aroum/PNCATEHO/doc/img/preview/3d_preview.jpg

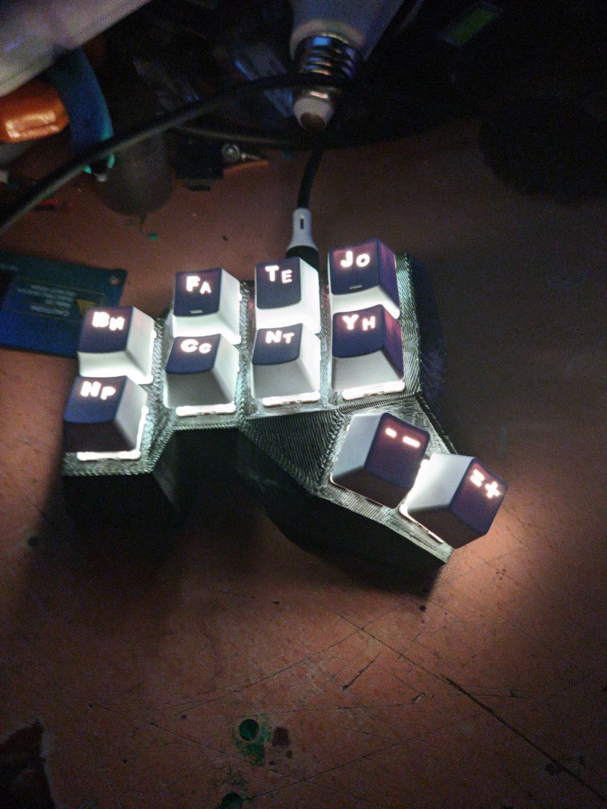
doc/img/preview/3d_preview.jpg
