aroum/PNCATEHO/doc/img/socket/machine_back.jpg

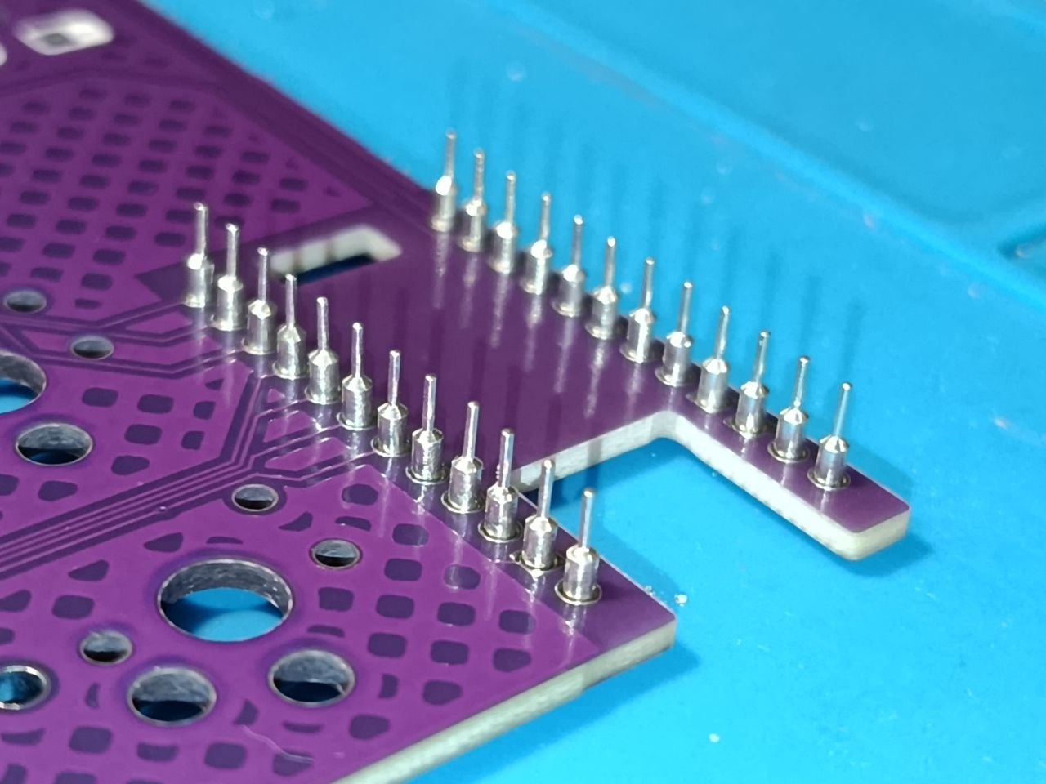
doc/img/socket/machine_back.jpg
