aroum/PNCATEHO/doc/img/socket/machine_back_mcu.jpg

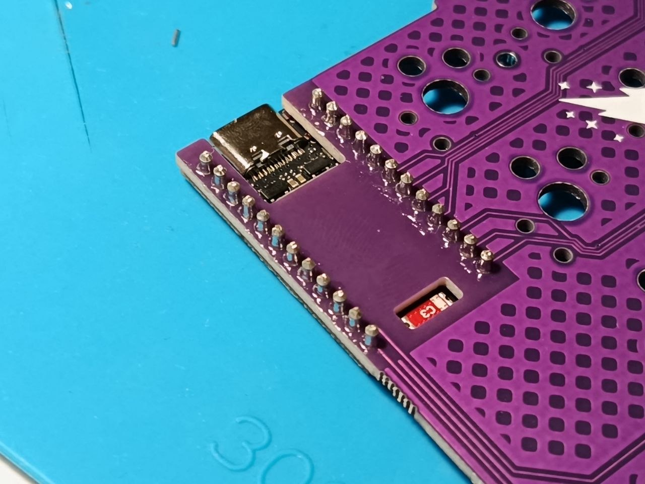
doc/img/socket/machine_back_mcu.jpg
