aroum/PNCATEHO/doc/img/socket/machine_back_strip.jpg

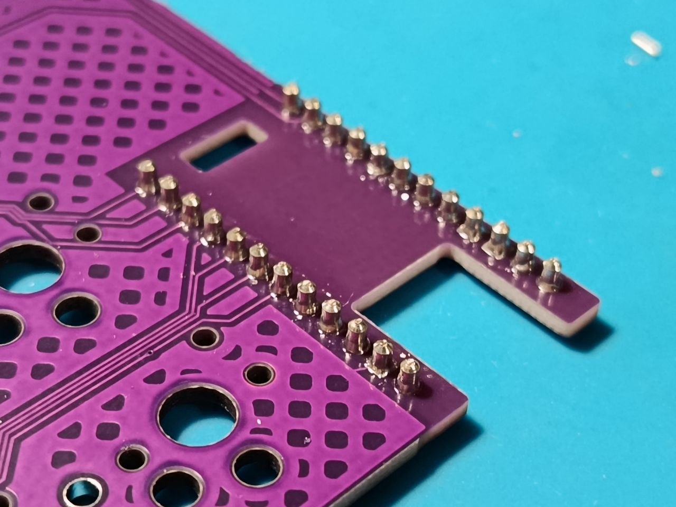
doc/img/socket/machine_back_strip.jpg
