aroum/PNCATEHO/doc/img/socket/machine_row.jpg

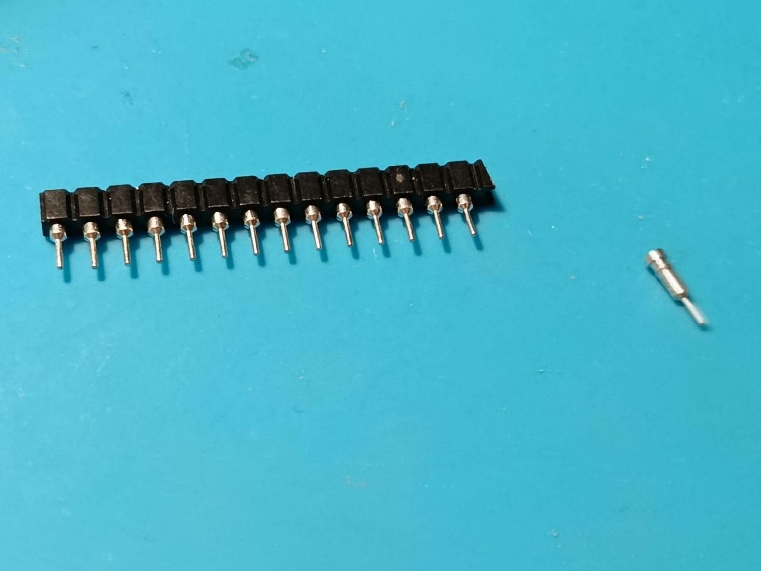
doc/img/socket/machine_row.jpg
