aroum/PNCATEHO/doc/img/socket/machine_top.jpg

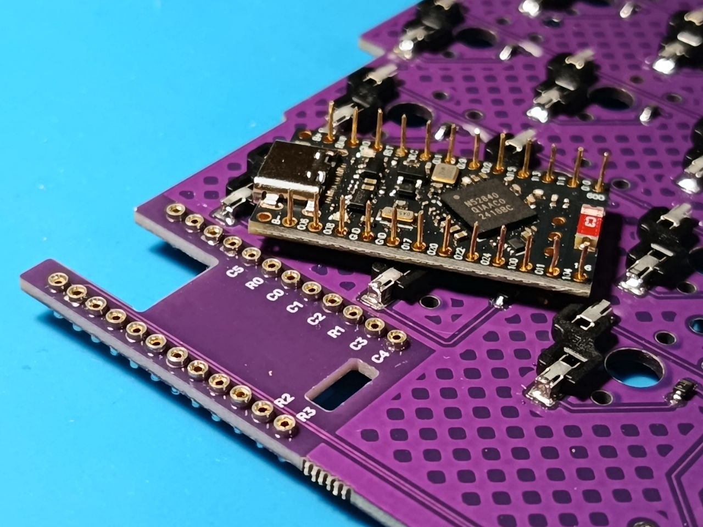
doc/img/socket/machine_top.jpg
