aroum/PNCATEHO/doc/img/socket/machine_top_mcu.jpg

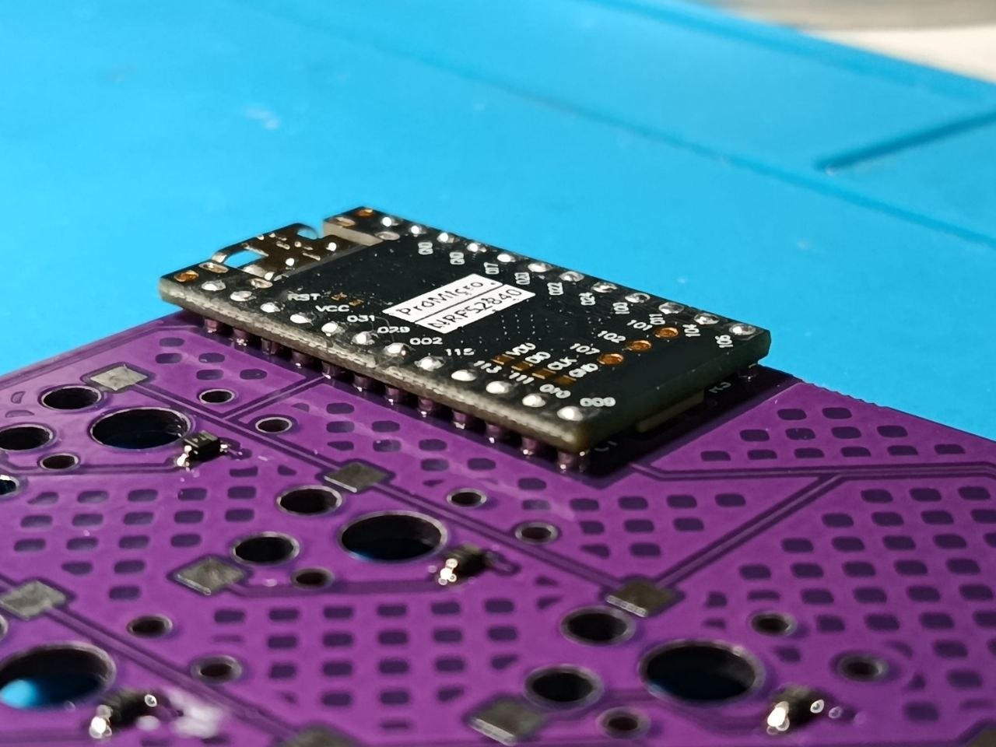
doc/img/socket/machine_top_mcu.jpg
