aroum/PNCATEHO/light/welcome/pcb/PNCATEHO_lib/step/SW_SPST_B3U-1000P-B.step

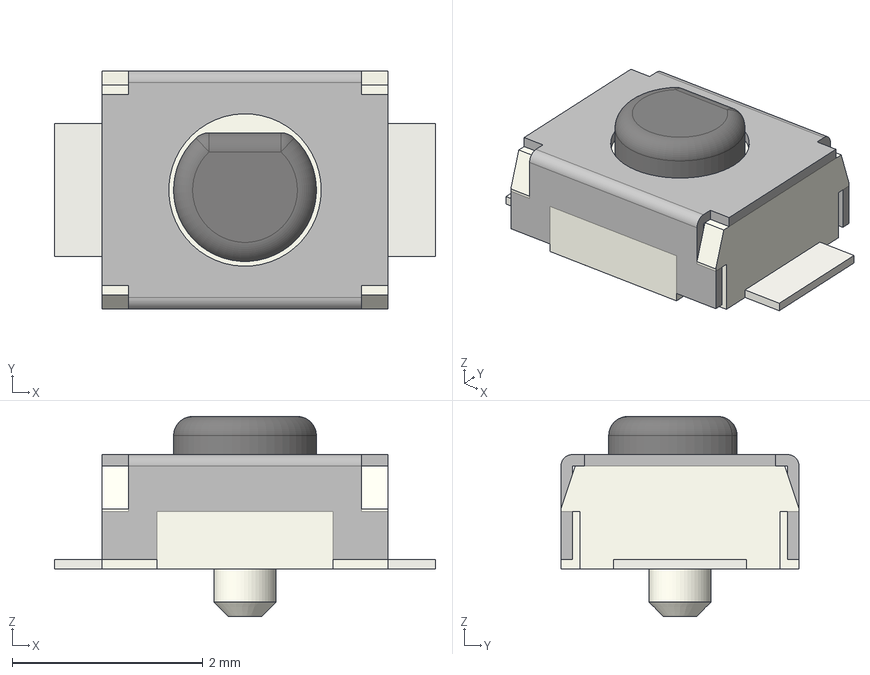
[picture p39: CAD file, 2026-05-25]
light/welcome/pcb/PNCATEHO_lib/step/SW_SPST_B3U-1000P-B.step
4.00 x 2.50 x 2.10 mm
