aroum/PNCATEHO/glass/case/MK_DOSE/PNCATEHO_MK_DOSE-case-bottom-right.step

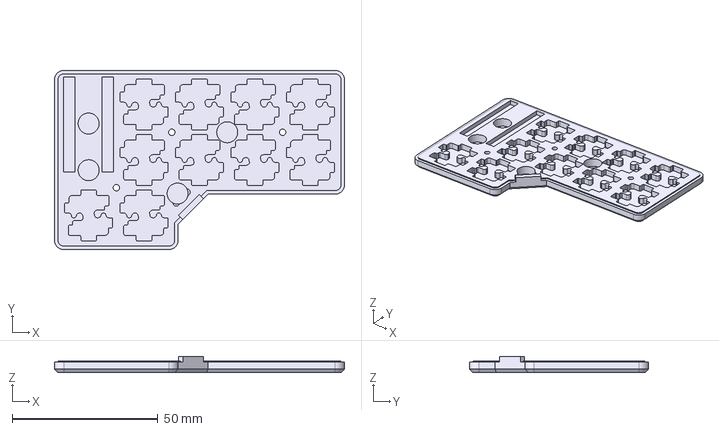
[picture p40: CAD file, 2025-08-24]
glass/case/MK_DOSE/PNCATEHO_MK_DOSE-case-bottom-right.step
99.4 x 61.4 x 5.60 mm
