aroum/PNCATEHO/glass/case/v5/PNCATEHO_v5-top-cover-left-PNCATEHO-ReggageOne.step

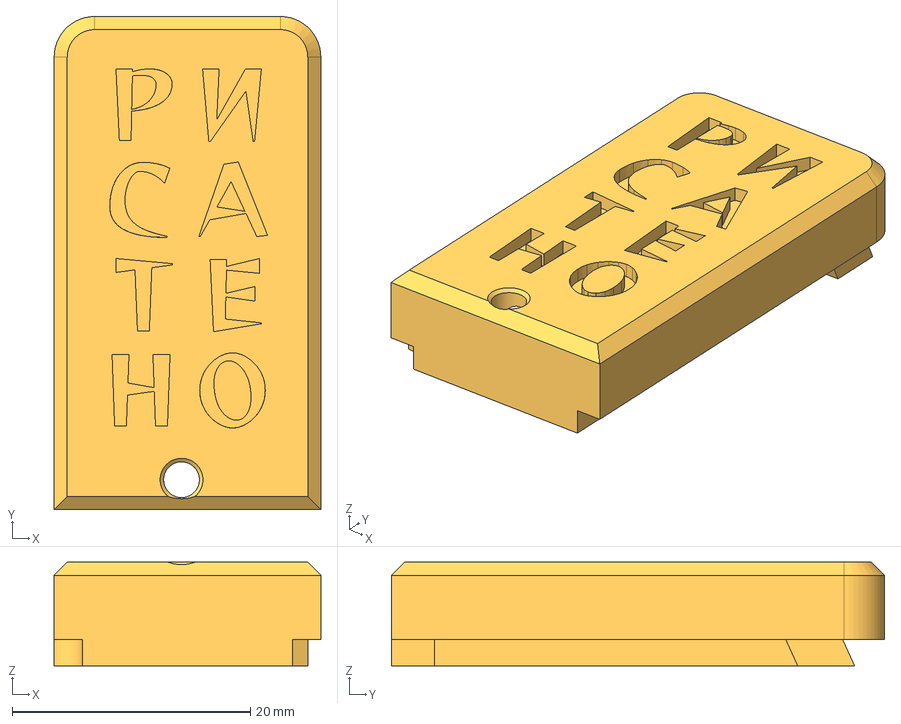
[picture p41: CAD file, 2025-06-07]
glass/case/v5/PNCATEHO_v5-top-cover-left-PNCATEHO-ReggageOne.step
22.4 x 41.4 x 8.70 mm
