aroum/PNCATEHO/light/welcome/pcb/PNCATEHO_lib/step/LED_0805_2012Metric.step

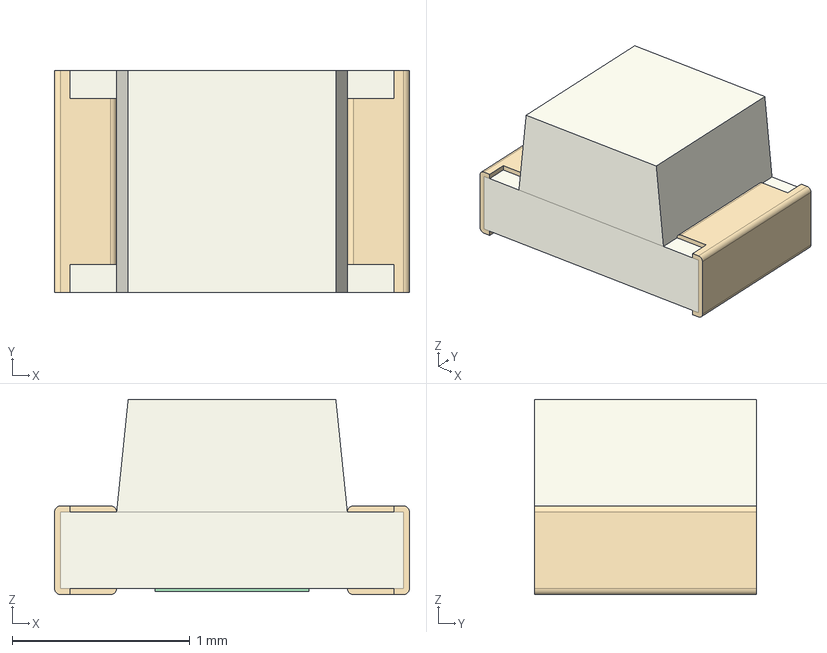
[picture p42: CAD file, 2026-05-25]
light/welcome/pcb/PNCATEHO_lib/step/LED_0805_2012Metric.step
2.00 x 1.25 x 1.10 mm
