aroum/PNCATEHO/light/welcome/pcb/PNCATEHO_lib/step/D_0805_2012Metric.step

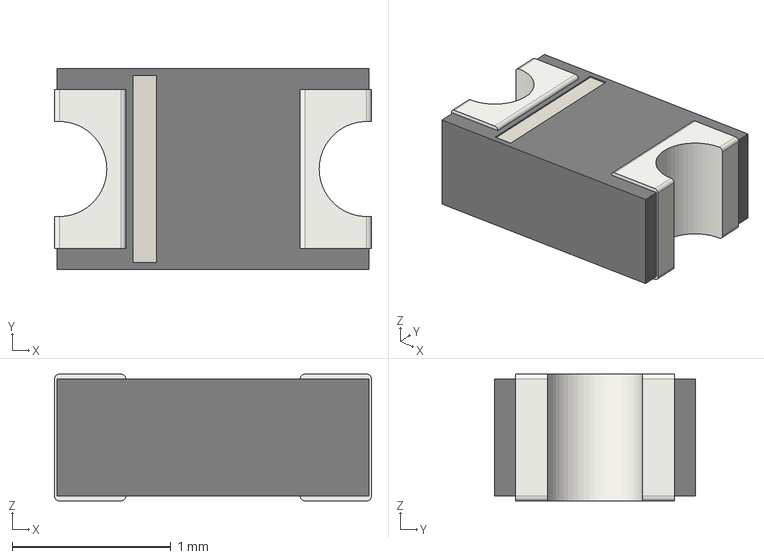
[picture p43: CAD file, 2026-05-25]
light/welcome/pcb/PNCATEHO_lib/step/D_0805_2012Metric.step
2.00 x 1.27 x 0.8 mm
