aroum/PNCATEHO/glass/case/MK_DOSE/PNCATEHO_MK_DOSE-case-top-left.step

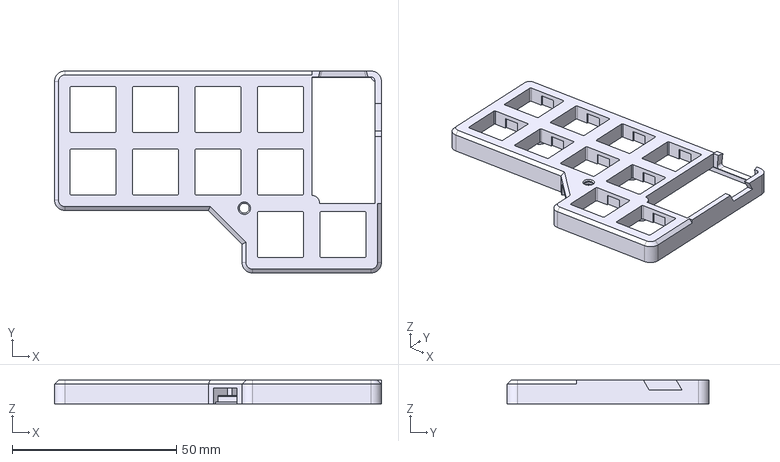
[picture p44: CAD file, 2025-08-12]
glass/case/MK_DOSE/PNCATEHO_MK_DOSE-case-top-left.step
99.4 x 61.4 x 7.20 mm
