aroum/PNCATEHO/glass/case/v5/PNCATEHO_v5-reset-button-pusher.step

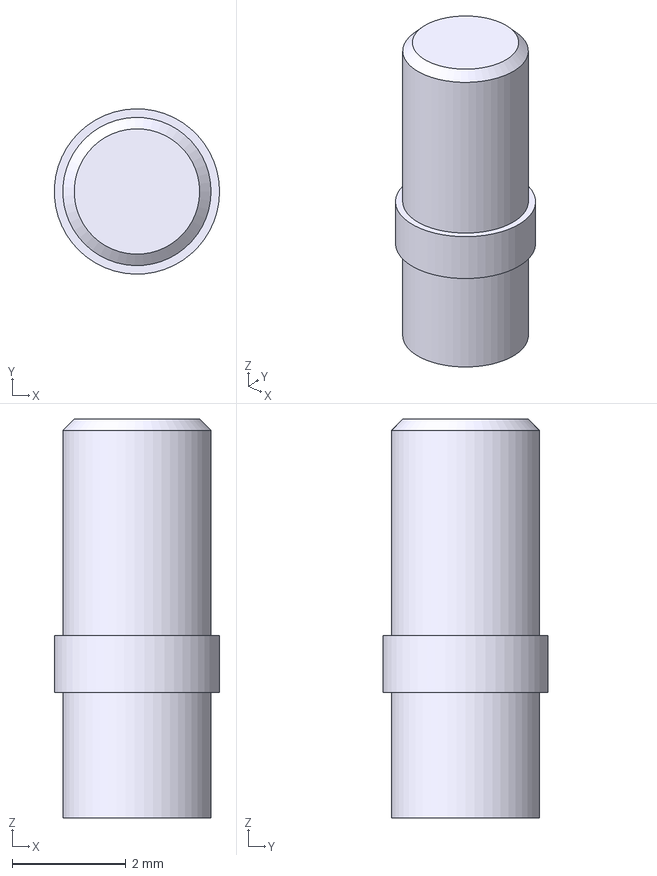
[picture p45: CAD file, 2025-06-07]
glass/case/v5/PNCATEHO_v5-reset-button-pusher.step
2.90 x 2.90 x 7.00 mm
