aroum/PNCATEHO/light/welcome/pcb/PNCATEHO_lib/step/R_0805_2012Metric.step

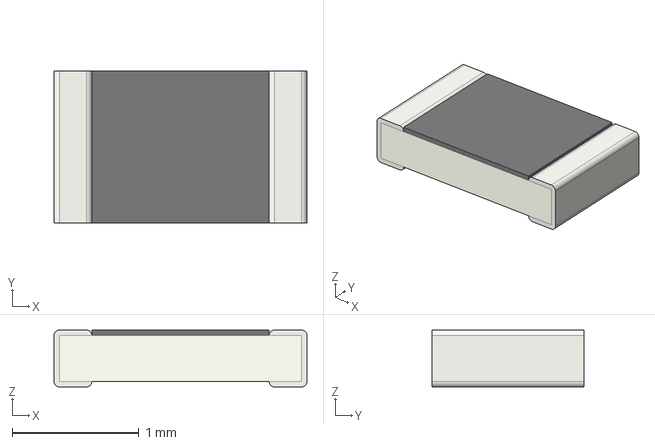
[picture p46: CAD file, 2026-05-25]
light/welcome/pcb/PNCATEHO_lib/step/R_0805_2012Metric.step
2.00 x 1.20 x 0.45 mm
