aroum/PNCATEHO/glass/case/MK_DOSE/PNCATEHO_MK_DOSE-case-top-cover-JP-katakana-right.step

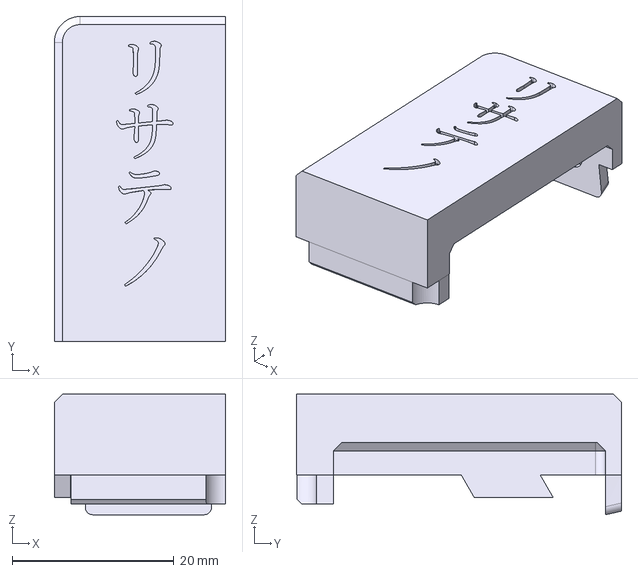
[picture p47: CAD file, 2025-08-12]
glass/case/MK_DOSE/PNCATEHO_MK_DOSE-case-top-cover-JP-katakana-right.step
21.2 x 40.2 x 14.9 mm
