aroum/PNCATEHO/glass/case/v5/PNCATEHO_v5-top-cover-right-blank.step

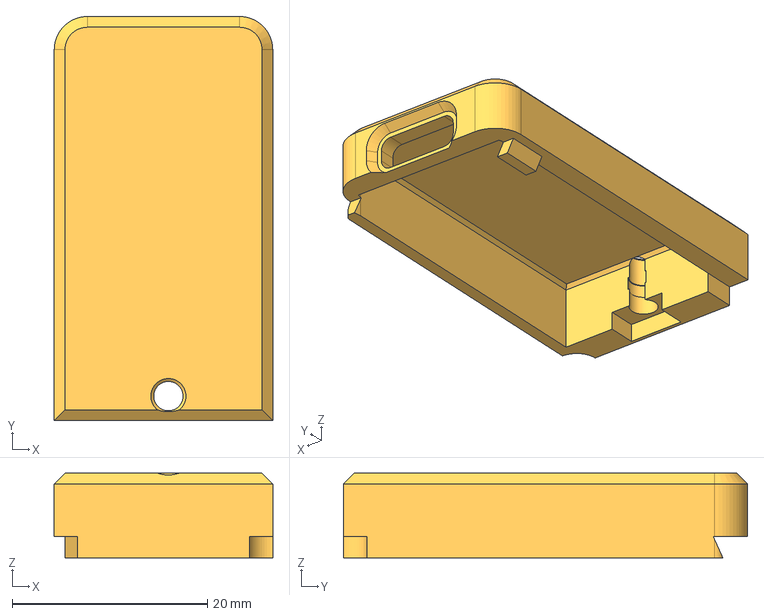
[picture p48: CAD file, 2025-06-07]
glass/case/v5/PNCATEHO_v5-top-cover-right-blank.step
22.4 x 41.4 x 8.70 mm
