aroum/PNCATEHO/light/welcome/pcb/PNCATEHO_lib/step/RT9013-33GB.STEP

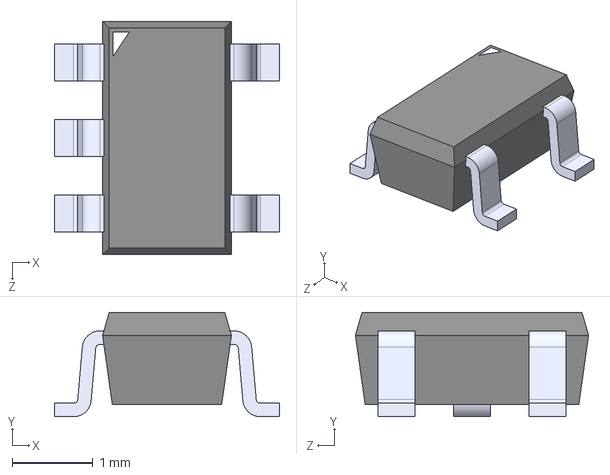
[picture p49: CAD file, 2026-05-25]
light/welcome/pcb/PNCATEHO_lib/step/RT9013-33GB.STEP
2.79 x 1.30 x 2.90 mm
