aroum/PNCATEHO/light/welcome/pcb/PNCATEHO_lib/step/PG1316S.STEP

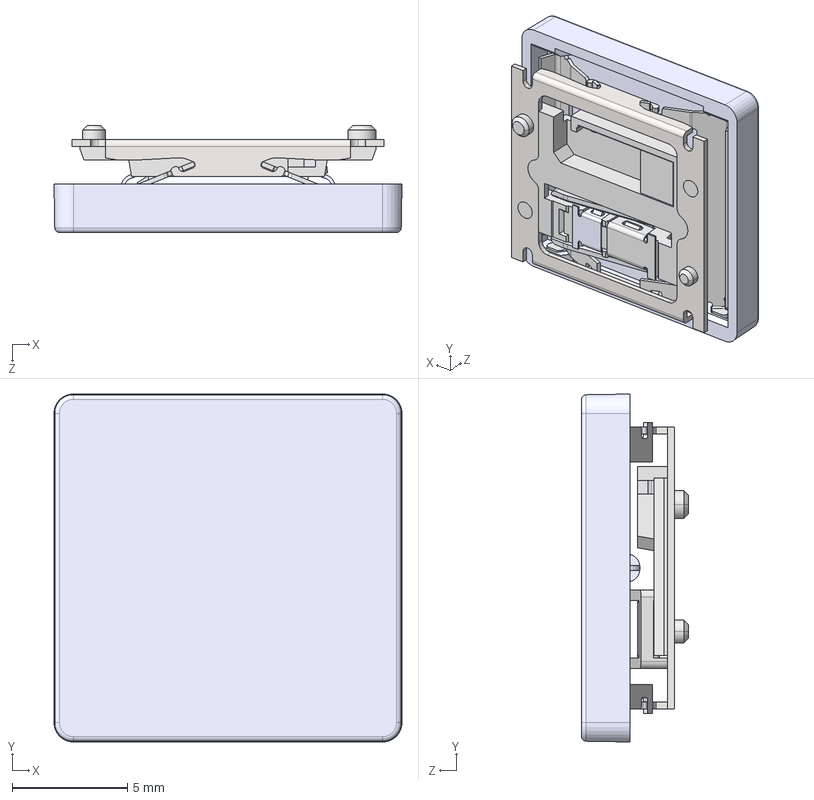
[picture p50: CAD file, 2026-05-25]
light/welcome/pcb/PNCATEHO_lib/step/PG1316S.STEP
15.1 x 15.1 x 4.63 mm
1316S-基座卡件
PG1316S-價釱
驱动杆
す算殤
嶺銅
PG1316S-动接触片-带触点
PG1316S-静片-带触点
す算殤-B
瑩簽
