aroum/PNCATEHO/glass/case/MK_DOSE/PNCATEHO_MK_DOSE-case-top-cover-blank-left.step

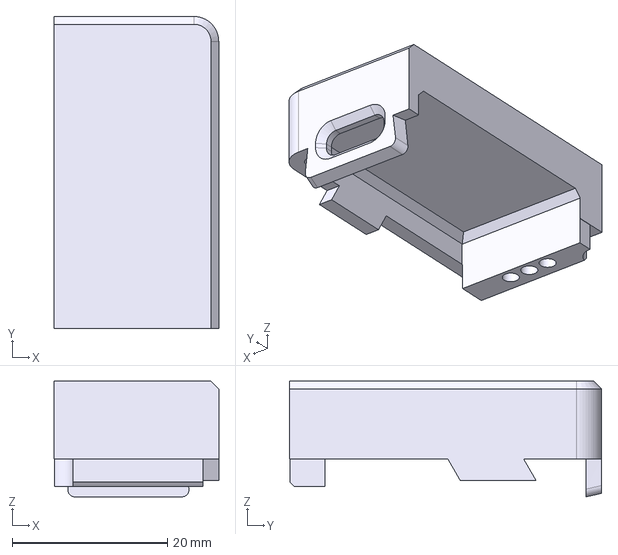
[picture p51: CAD file, 2025-08-12]
glass/case/MK_DOSE/PNCATEHO_MK_DOSE-case-top-cover-blank-left.step
21.2 x 40.2 x 14.9 mm
