aroum/PNCATEHO/light/welcome/pcb/PNCATEHO_lib/step/Crystal_SMD_3225-4Pin_3.2x2.5mm.step

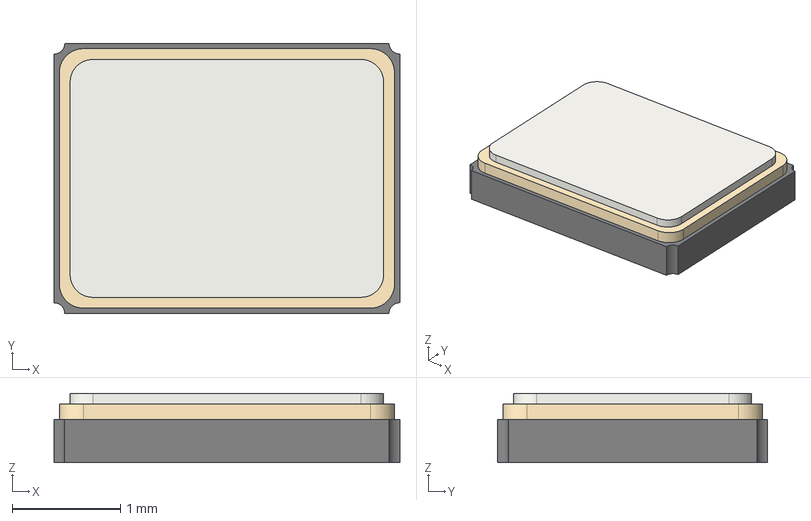
[picture p52: CAD file, 2026-05-25]
light/welcome/pcb/PNCATEHO_lib/step/Crystal_SMD_3225-4Pin_3.2x2.5mm.step
3.20 x 2.50 x 0.64 mm
