aroum/PNCATEHO/glass/case/v5/PNCATEHO_v5-power-switch-pusher.step

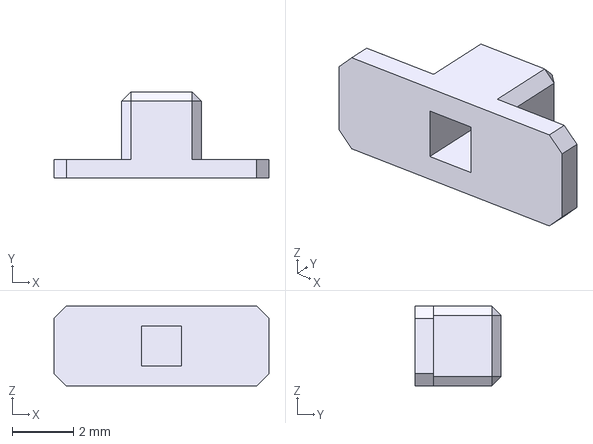
[picture p53: CAD file, 2025-06-07]
glass/case/v5/PNCATEHO_v5-power-switch-pusher.step
7.00 x 2.80 x 2.60 mm
