aroum/PNCATEHO/light/welcome/pcb/PNCATEHO_lib/step/QFN-56-1EP_7x7mm_P0.4mm_EP4x4mm.step

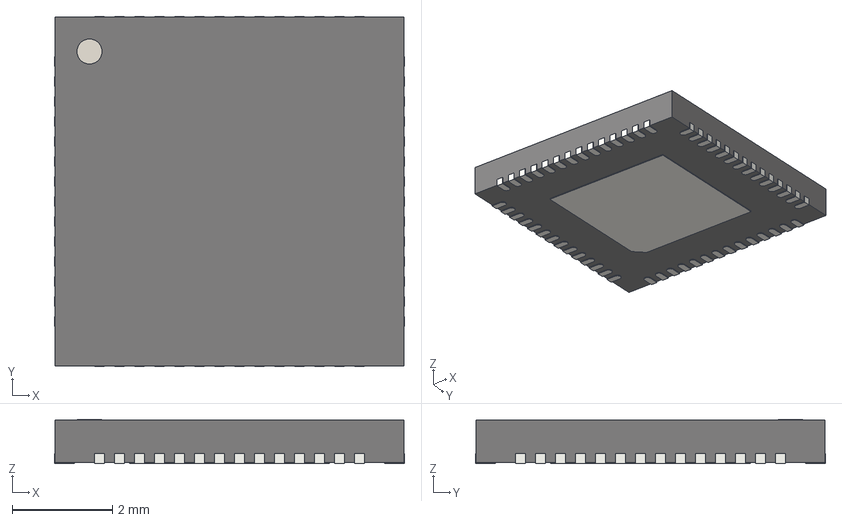
[picture p54: CAD file, 2026-05-25]
light/welcome/pcb/PNCATEHO_lib/step/QFN-56-1EP_7x7mm_P0.4mm_EP4x4mm.step
7.00 x 7.00 x 0.885 mm
a48c614c-8773-11ed-8f9d-58fb8493fcfb_part
a48c63fe-8773-11ed-8f9d-58fb8493fcfb_part
a48c65a2-8773-11ed-8f9d-58fb8493fcfb_part
a48c66d8-8773-11ed-8f9d-58fb8493fcfb_part
