aroum/PNCATEHO/glass/case/MK_DOSE/PNCATEHO_MK_DOSE-reset-button-pusher.step

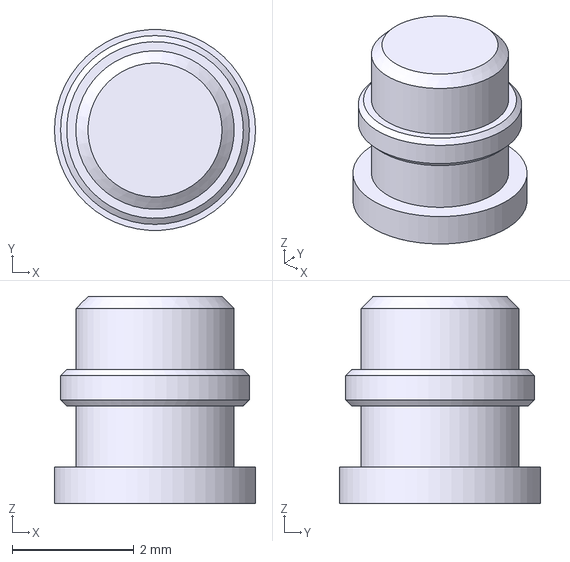
[picture p55: CAD file, 2025-08-12]
glass/case/MK_DOSE/PNCATEHO_MK_DOSE-reset-button-pusher.step
3.30 x 3.29 x 3.40 mm
