aroum/PNCATEHO/light/welcome/pcb/PNCATEHO_lib/step/W25Q32JVSSIQ--3DModel-STEP-269445.STEP

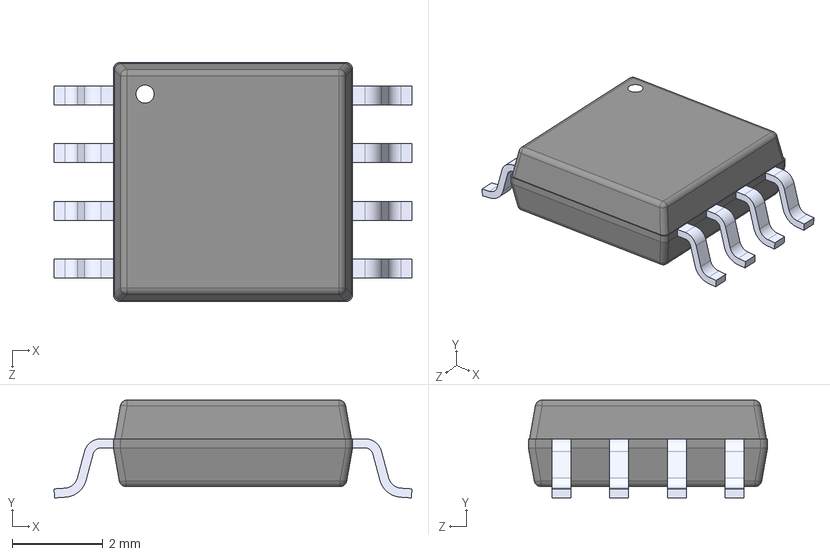
[picture p56: CAD file, 2026-05-25]
light/welcome/pcb/PNCATEHO_lib/step/W25Q32JVSSIQ--3DModel-STEP-269445.STEP
7.90 x 2.16 x 5.28 mm
