aroum/PNCATEHO/doc/img/build/glass/v5/hotswap_solder.jpg

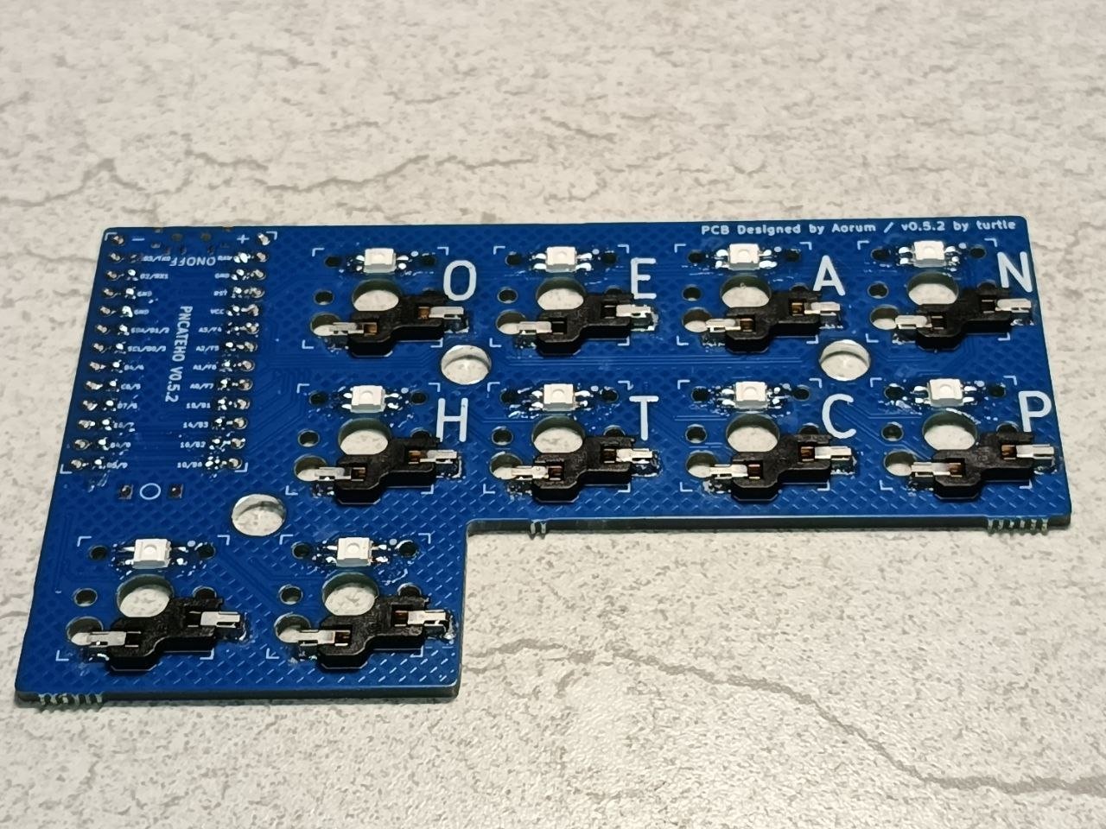
doc/img/build/glass/v5/hotswap_solder.jpg
