aroum/PNCATEHO/pcb/pcb_PNCATEHO_rgb/PNCATEHO_left.sch

## KiCad design pcb/pcb_PNCATEHO_rgb/PNCATEHO_left.sch (2021-08-10)

Schematic: PNCATEHO_left.sch

Parts:
LED1, LED2, LED3, LED4, LED5, LED6, LED7, LED8, LED9, LED10: YS-SK6812MINI-E
RSW1: SW_PUSH; SW_3x4x2_2legs
SW1, SW2, SW3, SW4, SW5, SW6, SW7, SW8, SW9, SW10: SW_PUSH; ChocV1
U1: ProMicro_r; ProMicro
